hendrickbg/covid19_mon_track/Firmware_Project/Vaccine_Tracker_BLE/Drivers/Peripherals_Drivers/Inc/bluenrg_lp_hal_flash.h

/**
******************************************************************************
* @file    bluenrg_lp_hal_flash.h
* @author  RF Application Team
* @brief   Header file of FLASH HAL module.
******************************************************************************
* @attention
*
* <h2><center>&copy; Copyright (c) 2018 STMicroelectronics. 
* All rights reserved.</center></h2>
*
* This software component is licensed by ST under BSD 3-Clause license,
* the "License"; You may not use this file except in compliance with the 
* License. You may obtain a copy of the License at:
*                        opensource.org/licenses/BSD-3-Clause
*
******************************************************************************
*/

/* Define to prevent recursive inclusion -------------------------------------*/
#ifndef BLUENRG_LP_HAL_FLASH_H
#define BLUENRG_LP_HAL_FLASH_H

#ifdef __cplusplus
extern "C" {
#endif
  
  /* Includes ------------------------------------------------------------------*/
#include "bluenrg_lp_hal_def.h"
  
  /** @addtogroup BLUENRG_LP_HAL_Driver
  * @{
  */
  
  /** @addtogroup FLASH
  * @{
  */
  
  /* Exported types ------------------------------------------------------------*/
  /** @defgroup FLASH_Exported_Types FLASH Exported Types
  * @{
  */
  
  /**
  * @brief  FLASH Erase structure definition
  */
  typedef struct
  {
    uint32_t TypeErase;   /*!< Mass erase or page erase.
    This parameter can be a value of @ref FLASH_TYPE_ERASE */
    uint32_t Page;        /*!< Initial Flash page to erase when page erase is enabled
    This parameter must be a value between 0 and (max number of pages - 1) */
    uint32_t NbPages;     /*!< Number of pages to be erased.
    This parameter must be a value between 1 and (max number of pages - value of initial page)*/
  } FLASH_EraseInitTypeDef;
  
  /**
  * @brief  FLASH handle Structure definition
  */
  typedef struct
  {
    HAL_LockTypeDef   Lock;              /* FLASH locking object */
    uint32_t          ErrorCode;         /* FLASH error code */
    uint32_t          ProcedureOnGoing;  /* Internal variable to indicate which procedure is ongoing or not in IT context */
    uint32_t          Address;           /* Internal variable to save address selected for program in IT context */
    uint32_t          Page;              /* Internal variable to define the current page which is erasing in IT context */
    uint32_t          NbPagesToErase;    /* Internal variable to save the remaining pages to erase in IT context */
  } FLASH_ProcessTypeDef;
  
  /**
  * @}
  */
  
  /* Exported constants --------------------------------------------------------*/
  /** @defgroup FLASH_Exported_Constants FLASH Exported Constants
  * @{
  */
  
  /** @defgroup FLASH_WAIT_STATES FLASH Wait States
  * @{
  */
#define FLASH_WAIT_STATES_0                 0x00000000UL                /*!< FLASH Zero wait state   */
#define FLASH_WAIT_STATES_1                 FLASH_CONFIG_WAIT_STATES_0  /*!< FLASH One wait state    */
  /**
  * @}
  */
  
  /** @defgroup FLASH_CONFIG_IRQ_VECT_TABLE FLASH Configuration Interrupt Vector Table 
  * @{
  */
#define FLASH_CONFIG_IRQ_VECT_TABLE_FLASH    FLASH_CONFIG_PREMAP  /*!< Vector Table located in FLASH */
#define FLASH_CONFIG_IRQ_VECT_TABLE_RAM      FLASH_CONFIG_REMAP   /*!< Vector Table located in RAM   */
  /**
  * @}
  */
  
  /** @defgroup FLASH_FLAGS FLASH Flags Definition
  * @{
  */
#define FLASH_FLAG_CMDDONE             FLASH_IRQRAW_CMDDONE_RIS     /*!< FLASH command done flag    */
#define FLASH_FLAG_CMDSTART            FLASH_IRQRAW_CMDSTART_RIS    /*!< FLASH command started flag */
#define FLASH_FLAG_CMDERR              FLASH_IRQRAW_CMDERR_RIS      /*!< FLASH command error flag   */
#define FLASH_FLAG_ILLCMD              FLASH_IRQRAW_ILLCMD_RIS      /*!< FLASH illegal command flag */
  
#define FLASH_FLAG_ALL_ERRORS          (FLASH_IRQRAW_CMDERR_RIS | FLASH_IRQRAW_ILLCMD_RIS)
  
  /** @defgroup FLASH_INTERRUPT_DEFINITION FLASH Interrupts Definition
  * @brief FLASH Interrupt definition
  * @{
  */
#define FLASH_IT_CMDDONE               FLASH_IRQMASK_CMDDONEM     /*!< FLASH command done Interrupt source */
#define FLASH_IT_CMDSTART              FLASH_IRQMASK_CMDSTARTM    /*!< FLASH command started Interrupt source */
#define FLASH_IT_CMDERR                FLASH_IRQMASK_CMDERRM      /*!< FLASH command error Interrupt source */
#define FLASH_IT_ILLCMD                FLASH_IRQMASK_ILLCMDM      /*!< FLASH illegal command Interrupt source */
  /**
  * @}
  */
  
  /** @defgroup FLASH_ERROR FLASH Error
  * @{
  */
#define HAL_FLASH_ERROR_NONE            0x00000000U
#define HAL_FLASH_ERROR_OP              FLASH_FLAG_CMDERR
#define HAL_FLASH_ERROR_ILLCMD          FLASH_FLAG_ILLCMD
  /**
  * @}
  */
  
  /** @defgroup FLASH_COMMAND FLASH Command
  * @{
  */
#define FLASH_CMD_ERASE_PAGES           0x11  /*!< flash pages erase command */
#define FLASH_CMD_MASSERASE             0x22  /*!< Flash mass erase command  */
#define FLASH_CMD_WRITE                 0x33  /*!< Flash write command       */
#define FLASH_CMD_BURSTWRITE            0xCC  /*!< Flash burst write command */
#define FLASH_CMD_OTPWRITE              0xEE  /*!< Flash OTP write command   */
  /**
  * @}
  */
  
  /** @defgroup FLASH_TYPE_ERASE FLASH Erase Type
  * @{
  */
#define FLASH_TYPE_ERASE_PAGES           0x00  /*!< Pages erase      */
#define FLASH_TYPE_ERASE_MASSERASE       0xFF  /*!< Flash mass erase */
  /**
  * @}
  */
  
  /** @defgroup FLASH_PAGEPROT_GROUP FLASH write/page erase protection for group
  * @{
  */
#define FLASH_PAGEPROT_GROUP_15           (0x8000UL)		/*!< write/page erase protection for group 15 containing Flash pages 120 to 127 */
#define FLASH_PAGEPROT_GROUP_14           (0x4000UL)		/*!< write/page erase protection for group 14 containing Flash pages 112 to 119 */		
#define FLASH_PAGEPROT_GROUP_13           (0x2000UL)		/*!< write/page erase protection for group 13 containing Flash pages 104 to 111 */
#define FLASH_PAGEPROT_GROUP_12           (0x1000UL)		/*!< write/page erase protection for group 12 containing Flash pages 96 to 103  */		
#define FLASH_PAGEPROT_GROUP_11           (0x800UL)		/*!< write/page erase protection for group 11 containing Flash pages 88 to 95   */
#define FLASH_PAGEPROT_GROUP_10           (0x400UL)		/*!< write/page erase protection for group 10 containing Flash pages 80 to 87   */
#define FLASH_PAGEPROT_GROUP_9            (0x200UL)		/*!< write/page erase protection for group 9  containing Flash pages 72 to 79   */
#define FLASH_PAGEPROT_GROUP_8            (0x100UL)		/*!< write/page erase protection for group 8  containing Flash pages 64 to 71   */
#define FLASH_PAGEPROT_GROUP_7            (0x80UL)		/*!< write/page erase protection for group 7  containing Flash pages 56 to 63   */
#define FLASH_PAGEPROT_GROUP_6            (0x40UL)		/*!< write/page erase protection for group 6  containing Flash pages 48 to 55   */
#define FLASH_PAGEPROT_GROUP_5            (0x20UL)		/*!< write/page erase protection for group 5  containing Flash pages 40 to 47   */
#define FLASH_PAGEPROT_GROUP_4            (0x10UL)		/*!< write/page erase protection for group 4  containing Flash pages 32 to 39   */
#define FLASH_PAGEPROT_GROUP_3            (0x8UL)		/*!< write/page erase protection for group 3  containing Flash pages 24 to 31   */
#define FLASH_PAGEPROT_GROUP_2            (0x4UL)		/*!< write/page erase protection for group 2  containing Flash pages 16 to 23   */	    	
#define FLASH_PAGEPROT_GROUP_1            (0x2UL)		/*!< write/page erase protection for group 1  containing Flash pages 8 to 15    */
#define FLASH_PAGEPROT_GROUP_0            (0x1UL)		/*!< write/page erase protection for group 0  containing Flash pages 0 to 7     */ 
    /**
    * @}
    */
    
  
/**
  * @brief  Page Protection function configuration structure definition
  */
typedef struct
{
  uint32_t pageProt_0;       /*!< For cut 1.0 indicate the group to configure.
                                  - This parameter can be a value of @ref FLASH_PAGEPROT_GROUP                   
                                  For cut 2.0 it is a bitfield built as follows:
                                  - bit[6:0]   = SIZE: number of 2 kB pages to protect including the starting page
                                                       @ref pageProt_0 param (provided in the offset bits)
                                  - bit[7]     = reserved
                                  - bit[14:8]  = OFFSET: page number to start the write protection 
                                                        (value between 0 and 0x7F)
                                  - bit[15]    = reserved
                                  - bit[22:16] = SIZE: same meaning of bit[6:0]
                                  - bit[23]    = reserved
                                  - bit[30:24] = OFFSET: same meaning of bit[22:16]
                                  - bit[31]    = reserved                                                           */
  uint32_t pageProt_1;       /*!< Valid only for cut 2.0 same meaning of @ref pageProt_0 parameter                  */
  FunctionalState state;     /*!< The new state of the group.
                                  This parameter can be a value of @ref FunctionalState                             */
} FLASH_PageProtectionTypeDef;

  
    /**
    * @}
    */
    
    /* Exported macros -----------------------------------------------------------*/
    /** @defgroup FLASH_Exported_Macros FLASH Exported Macros
    *  @brief macros to control FLASH features
    *  @{
    */
    
    /**
    * @brief  Set the FLASH Wait States.
    * @param __WAIT_STATES__ FLASH WAIT States
    *         This parameter can be one of the following values :
    *     @arg @ref FLASH_WAIT_STATES_0 FLASH Zero wait state
    *     @arg @ref FLASH_WAIT_STATES_1 FLASH One wait state
    * @retval None
    */
#define __HAL_FLASH_SET_WAIT_STATES(__WAIT_STATES__)    MODIFY_REG(FLASH->CONFIG, FLASH_CONFIG_WAIT_STATES, (__WAIT_STATES__))
    
    /**
    * @brief  Get the FLASH Wait States.
    * @retval FLASH Wait States
    *         Returned value can be one of the following values :
    *     @arg @ref FLASH_WAIT_STATES_0 FLASH Zero wait state
    *     @arg @ref FLASH_WAIT_STATES_1 FLASH One wait state
    */ 
#define __HAL_FLASH_GET_WAIT_STATES()               READ_BIT(FLASH->CONFIG, FLASH_CONFIG_WAIT_STATES)
    
    /**
    * @brief  Enable the FLASH burst write operations.
    * @retval None
    */
#define __HAL_FLASH_BURSTWRITE_ENABLE()    CLEAR_BIT(FLASH->CONFIG, FLASH_CONFIG_DIS_GROUP_WRITE)
    
    /**
    * @brief  Disable the FLASH burst write operations.
    * @retval None
    */
#define __HAL_FLASH_BURSTWRITE_DISABLE()    SET_BIT(FLASH->CONFIG, FLASH_CONFIG_DIS_GROUP_WRITE)
    
    /**
    * @brief  Set the FLASH Interrupt Vector Table location.
    * @param __VECT_TABLE__ Vector Table Configuration
    *         This parameter can be one of the following values :
    *     @arg @ref FLASH_CONFIG_IRQ_VECT_TABLE_FLASH Vector Table located in FLASH
    *     @arg @ref FLASH_CONFIG_IRQ_VECT_TABLE_RAM   Vector Table located in RAM
    * @retval None
    */
#define __HAL_FLASH_SET_VECT_TABLE(__VECT_TABLE__)    MODIFY_REG(FLASH->CONFIG, FLASH_CONFIG_PREMAP|FLASH_CONFIG_REMAP, (__VECT_TABLE__))
    
    /**
    * @brief  Get the FLASH Interrupt Vector Table location.
    * @retval Vector Table Configuration
    *         Returned value can be one of the following values :
    *     @arg @ref FLASH_CONFIG_IRQ_VECT_TABLE_FLASH Vector Table located in FLASH
    *     @arg @ref FLASH_CONFIG_IRQ_VECT_TABLE_RAM   Vector Table located in RAM
    */ 
#define __HAL_FLASH_GET_VECT_TABLE()               READ_BIT(FLASH->CONFIG, FLASH_CONFIG_PREMAP|FLASH_CONFIG_REMAP)
    
    /**
    * @}
    */
    
    /** @defgroup FLASH_Interrupt FLASH Interrupts Macros
    *  @brief macros to handle FLASH interrupts
    * @{
    */
    
    /**
    * @brief  Enable the specified FLASH interrupt.
    * @param __INTERRUPT__ FLASH interrupt
    *         This parameter can be any combination of the following values:
    *     @arg @ref FLASH_IT_CMDDONE  Command Done Interrupt
    *     @arg @ref FLASH_IT_CMDSTART Command Started Interrupt
    *     @arg @ref FLASH_IT_CMDERR   Command Error Interrupt
    *     @arg @ref FLASH_IT_ILLCMD   Illegal Command Interrupt
    * @retval none
    */
#define __HAL_FLASH_ENABLE_IT(__INTERRUPT__)    SET_BIT(FLASH->IRQMASK, (__INTERRUPT__))
    
    /**
    * @brief  Disable the specified FLASH interrupt.
    * @param __INTERRUPT__ FLASH interrupt
    *         This parameter can be any combination of the following values:
    *     @arg @ref FLASH_IT_CMDDONE  Command Done Interrupt
    *     @arg @ref FLASH_IT_CMDSTART Command Started Interrupt
    *     @arg @ref FLASH_IT_CMDERR   Command Error Interrupt
    *     @arg @ref FLASH_IT_ILLCMD   Illegal Command Interrupt
    * @retval none
    */
#define __HAL_FLASH_DISABLE_IT(__INTERRUPT__)   CLEAR_BIT(FLASH->IRQMASK, (__INTERRUPT__))
    
    /**
    * @brief  Check whether the specified FLASH interrupt has occurred or not.
    * @param __INTERRUPT__ FLASH interrupt
    *         This parameter can be any combination of the following values:
    *     @arg @ref FLASH_IT_CMDDONE  Command Done Interrupt
    *     @arg @ref FLASH_IT_CMDSTART Command Started Interrupt
    *     @arg @ref FLASH_IT_CMDERR   Command Error Interrupt
    *     @arg @ref FLASH_IT_ILLCMD   Illegal Command Interrupt
    * @retval The new state of __INTERRUPT__ (SET or RESET).
    */
#define __HAL_FLASH_GET_IT(__INTERRUPT__)   ((READ_BIT(FLASH->IRQSTAT, (__INTERRUPT__)) != RESET) ? SET : RESET)
    
    /**
    * @brief Clear the specified FLASH interrupt flag.
    * @param __INTERRUPT__ FLASH interrupt
    *         This parameter can be any combination of the following values:
    *     @arg @ref FLASH_IT_CMDDONE  Command Done Interrupt
    *     @arg @ref FLASH_IT_CMDSTART Command Started Interrupt
    *     @arg @ref FLASH_IT_CMDERR   Command Error Interrupt
    *     @arg @ref FLASH_IT_ILLCMD   Illegal Command Interrupt
    * @retval None
    */
#define __HAL_FLASH_CLEAR_IT(__INTERRUPT__)   SET_BIT(FLASH->IRQSTAT, (__INTERRUPT__))
    
    /**
    * @brief  Check whether the specified FLASH flag is set or not.
    * @param __FLAG__ specifies the FLASH flag to check.
    *   This parameter can be one of the following values:
    *     @arg @ref FLASH_FLAG_CMDDONE     FLASH command done flag
    *     @arg @ref FLASH_FLAG_CMDSTART    FLASH command started flag
    *     @arg @ref FLASH_FLAG_CMDERR      FLASH command error flag
    *     @arg @ref FLASH_FLAG_ILLCMD      FLASH illegal command flag
    * @retval The new state of FLASH_FLAG (SET or RESET).
    */
#define __HAL_FLASH_GET_FLAG(__FLAG__)  ((READ_BIT(FLASH->IRQRAW, (__FLAG__)) == (__FLAG__)) ? 1UL : 0UL)
    
    /**
    * @brief  Clear the FLASH's pending flags.
    * @param __FLAG__ specifies the FLASH flags to clear.
    *   This parameter can be any combination of the following values:
    *     @arg @ref FLASH_FLAG_CMDDONE     FLASH command done flag
    *     @arg @ref FLASH_FLAG_CMDSTART    FLASH command started flag
    *     @arg @ref FLASH_FLAG_CMDERR      FLASH command error flag
    *     @arg @ref FLASH_FLAG_ILLCMD      FLASH illegal command flag
    * @retval None
    */
#define __HAL_FLASH_CLEAR_FLAG(__FLAG__) (SET_BIT(FLASH->IRQRAW, (__FLAG__)))
    /**
    * @}
    */
    
    /* Include FLASH HAL Extended module */
#include "bluenrg_lp_hal_flash_ex.h"
    
    /* Exported variables --------------------------------------------------------*/
    /** @defgroup FLASH_Exported_Variables FLASH Exported Variables
    * @{
    */
    extern FLASH_ProcessTypeDef pFlash;
  /**
  * @}
  */
  
  /* Exported functions --------------------------------------------------------*/
  /** @addtogroup FLASH_Exported_Functions
  * @{
  */
  
  /* Program operation functions  ***********************************************/
  /** @addtogroup FLASH_Exported_Functions_Group1
  * @{
  */
  HAL_StatusTypeDef  HAL_FLASH_Program(uint32_t Address, uint32_t Data);
  HAL_StatusTypeDef  HAL_FLASH_Program_IT(uint32_t Address, uint32_t Data);
  HAL_StatusTypeDef  HAL_FLASH_ProgramBurst(uint32_t Address, uint32_t *Data);
  HAL_StatusTypeDef  HAL_FLASH_ProgramBurst_IT(uint32_t Address, uint32_t *Data);
  /* FLASH IRQ handler method */
  void               HAL_FLASH_IRQHandler(void);
  /* Callbacks in non blocking modes */
  void               HAL_FLASH_EndOfOperationCallback(uint32_t ReturnValue);
  void               HAL_FLASH_OperationErrorCallback(uint32_t ReturnValue);
  /**
  * @}
  */
  
  /* Peripheral State functions  ************************************************/
  /** @addtogroup FLASH_Exported_Functions_Group2
  * @{
  */
  uint32_t HAL_FLASH_GetError(void);
  /**
  * @}
  */
  
  /**
  * @}
  */
  
  /* Private types --------------------------------------------------------*/
  /** @defgroup FLASH_Private_types FLASH Private Types
  * @{
  */
  HAL_StatusTypeDef  FLASH_WaitForLastOperation(uint32_t Timeout);
  /**
  * @}
  */
  
  /* Private constants --------------------------------------------------------*/
  /** @defgroup FLASH_Private_Constants FLASH Private Constants
  * @{
  */
#define FLASH_SIZE                      (((*(uint32_t *)FLASHSIZE_BASE & 0xFFFF) + 1) << 2U)
#define FLASH_START_ADDR                NVM_BASE
#define FLASH_END_ADDR                  (FLASH_START_ADDR + FLASH_SIZE - 1U)
 
 
#define FLASH_PAGE_SIZE                 0x00000800U  /*!< FLASH Page Size, 2KBytes */
#define FLASH_PAGE_NUMBER               (FLASH_SIZE/FLASH_PAGE_SIZE )
#define FLASH_TIMEOUT_VALUE             1000U        /*!< FLASH Execution Timeout, 1 s */
  
#define FLASH_WRERP_GRANULARITY         0x00004000U  /*!< FLASH Write/Erase Protection Granularity, 16KBytes */
#define FLASH_PCROP_GRANULARITY         FLASH_SIZE   /*!< FLASH Code Readout Protection Granularity, all the MAIN FLASH */
  
#define FLASH_TYPENONE                  0x00000000u  /*!< No Programming Procedure On Going */
  
  /**
  * @}
  */
  
  /* Private macros ------------------------------------------------------------*/
  /** @defgroup FLASH_Private_Macros FLASH Private Macros
  *  @{
  */
  
#define IS_FLASH_MAIN_MEM_ADDRESS(__VALUE__)        (((__VALUE__) >= FLASH_START_ADDR) && ((__VALUE__) <= FLASH_END_ADDR))
  
#define IS_FLASH_PROGRAM_MAIN_MEM_ADDRESS(__VALUE__)   (((__VALUE__) >= FLASH_START_ADDR) && ((__VALUE__) <= (FLASH_START_ADDR + FLASH_SIZE - 4UL)) && (((__VALUE__) % 4UL) == 0UL))
  
#define IS_FLASH_PROGRAM_OTP_ADDRESS(__VALUE__)     (((__VALUE__) >= OTP_AREA_BASE) && ((__VALUE__) <= (OTP_AREA_END_ADDR + 1UL - 4UL)) && (((__VALUE__) % 4UL) == 0UL))
  
#define IS_FLASH_PROGRAM_ADDRESS(__VALUE__)         ((IS_FLASH_PROGRAM_MAIN_MEM_ADDRESS(__VALUE__)) || (IS_FLASH_PROGRAM_OTP_ADDRESS(__VALUE__)))
  
#define IS_FLASH_PAGE(__VALUE__)                    ((__VALUE__) <= FLASH_PAGE_NUMBER)
  
#define IS_ADDR_ALIGNED_32BITS(__VALUE__)           (((__VALUE__) & ~0x3U) == (__VALUE__))
  
#define IS_FLASH_WAIT_STATES(__VALUE__)              (((__VALUE__) == FLASH_WAIT_STATES_0) || \
  ((__VALUE__) == FLASH_WAIT_STATES_1))

#define IS_FLASH_TYPE_ERASE(__VALUE__)               (((__VALUE__) == FLASH_TYPE_ERASE_PAGES) || \
((__VALUE__) == FLASH_TYPE_ERASE_MASSERASE))

/**
* @}
*/

/**
* @}
*/

/**
* @}
*/

#ifdef __cplusplus
}
#endif

#endif /* BLUENRG_LP_HAL_FLASH_H */

/************************ (C) COPYRIGHT STMicroelectronics *****END OF FILE****/
