hendrickbg/covid19_mon_track/Firmware_Project/Vaccine_Tracker_BLE/Drivers/Peripherals_Drivers/Src/bluenrg_lp_hal.c

/**
  ******************************************************************************
  * @file    bluenrg_lp_hal.c
  * @author  RF Application Team
  * @brief   HAL module driver.
  *          This is the common part of the HAL initialization
  *
  @verbatim
  ==============================================================================
                     ##### How to use this driver #####
  ==============================================================================
    [..]
    The common HAL driver contains a set of generic and common APIs that can be
    used by the PPP peripheral drivers and the user to start using the HAL.
    [..]
    The HAL contains two APIs' categories:
         (+) Common HAL APIs
         (+) Services HAL APIs

  @endverbatim
  ******************************************************************************
  * @attention
  *
  * <h2><center>&copy; Copyright (c) 2018 STMicroelectronics. 
  * All rights reserved.</center></h2>
  *
  * This software component is licensed by ST under BSD 3-Clause license,
  * the "License"; You may not use this file except in compliance with the 
  * License. You may obtain a copy of the License at:
  *                        opensource.org/licenses/BSD-3-Clause
  *
  ******************************************************************************
  */

/* Includes ------------------------------------------------------------------*/
#include "bluenrg_lp_hal.h"

/** @addtogroup BLUENRG_LP_HAL_Driver
  * @{
  */

/** @addtogroup HAL
  * @brief HAL module driver
  * @{
  */

#ifdef HAL_MODULE_ENABLED

/* Private typedef -----------------------------------------------------------*/
/* Private define ------------------------------------------------------------*/

/** @defgroup HAL_Private_Constants HAL Private Constants
  * @{
  */
/**
 * @brief BLUENRG_LP HAL Driver version number
   */
#define __BLUENRG_LP_HAL_VERSION_MAIN   (0x00U) /*!< [31:24] main version */
#define __BLUENRG_LP_HAL_VERSION_SUB1   (0x00U) /*!< [23:16] sub1 version */
#define __BLUENRG_LP_HAL_VERSION_SUB2   (0x0DU) /*!< [15:8]  sub2 version */
#define __BLUENRG_LP_HAL_VERSION_RC     (0x00U) /*!< [7:0]  release candidate */
#define __BLUENRG_LP_HAL_VERSION         ((__BLUENRG_LP_HAL_VERSION_MAIN << 24U)\
                                        |(__BLUENRG_LP_HAL_VERSION_SUB1 << 16U)\
                                        |(__BLUENRG_LP_HAL_VERSION_SUB2 << 8U )\
                                        |(__BLUENRG_LP_HAL_VERSION_RC))

/**
  * @}
  */

/* Private macro -------------------------------------------------------------*/
/* Exported variables ---------------------------------------------------------*/
/** @defgroup HAL_Exported_Variables HAL Exported Variables
  * @{
  */
__IO uint32_t uwTick;
uint32_t uwTickPrio = (1UL << __NVIC_PRIO_BITS); /* Invalid PRIO */
uint32_t uwTickFreq = HAL_TICK_FREQ_DEFAULT;  /* 1KHz */
/**
  * @}
  */

/* Private function prototypes -----------------------------------------------*/
/* Exported functions --------------------------------------------------------*/

/** @addtogroup HAL_Exported_Functions
  * @{
  */

/** @addtogroup HAL_Exported_Functions_Group1
 *  @brief    HAL Initialization and Configuration functions
 *
@verbatim
 ===============================================================================
           ##### HAL Initialization and Configuration functions #####
 ===============================================================================
    [..]  This section provides functions allowing to:
      (+) Initialize the Flash interface the NVIC allocation and initial time base
          clock configuration.
      (+) De-initialize common part of the HAL.
      (+) Configure the time base source to have 1ms time base with a dedicated
          Tick interrupt priority.
        (++) SysTick timer is used by default as source of time base, but user
             can eventually implement his proper time base source (a general purpose
             timer for example or other time source), keeping in mind that Time base
             duration should be kept 1ms since PPP_TIMEOUT_VALUEs are defined and
             handled in milliseconds basis.
        (++) Time base configuration function (HAL_InitTick ()) is called automatically
             at the beginning of the program after reset by HAL_Init() or at any time
             when clock is configured, by HAL_RCC_ClockConfig().
        (++) Source of time base is configured  to generate interrupts at regular
             time intervals. Care must be taken if HAL_Delay() is called from a
             peripheral ISR process, the Tick interrupt line must have higher priority
            (numerically lower) than the peripheral interrupt. Otherwise the caller
            ISR process will be blocked.
       (++) functions affecting time base configurations are declared as __weak
             to make  override possible  in case of other  implementations in user file.
@endverbatim
  * @{
  */

/**
  * @brief  This function is used to initialize the HAL Library; it must be the first
  *         instruction to be executed in the main program (before to call any other
  *         HAL function), it performs the following:
  *           Configures the SysTick to generate an interrupt each 1 millisecond,
  *           which is clocked by the System Clock.
  *           Calls the HAL_MspInit() callback function defined in user file
  *           "bluenrg_lp_hal_msp.c" to do the global low level hardware initialization
  *
  * @note   SysTick is used as time base for the HAL_Delay() function, the application
  *         need to ensure that the SysTick time base is always set to 1 millisecond
  *         to have correct HAL operation.
  * @retval HAL status
  */
HAL_StatusTypeDef HAL_Init(void)
{
  HAL_StatusTypeDef  status = HAL_OK;
  
  /* Use SysTick as time base source and configure 1ms tick (default clock after Reset is MSI) */
  if (HAL_InitTick(TICK_INT_PRIORITY) != HAL_OK)
  {
    status = HAL_ERROR;
  }
  else
  {
    /* Init the low level hardware */
    HAL_MspInit();
  }

  /* Return function status */
  return status;
}

/**
  * @brief  This function de-Initializes common part of the HAL and stops the source of time base.
  * @note   This function is optional.
  * @retval HAL status
  */
HAL_StatusTypeDef HAL_DeInit(void)
{
  /* Reset of all peripherals */
  __HAL_RCC_AHB_FORCE_RESET();
  __HAL_RCC_AHB_RELEASE_RESET();

  __HAL_RCC_APB0_FORCE_RESET();
  __HAL_RCC_APB0_RELEASE_RESET();

  __HAL_RCC_APB1_FORCE_RESET();
  __HAL_RCC_APB1_RELEASE_RESET();

  __HAL_RCC_APB2_FORCE_RESET();
  __HAL_RCC_APB2_RELEASE_RESET();

  /* De-Init the low level hardware */
  HAL_MspDeInit();

  /* Return function status */
  return HAL_OK;
}

/**
  * @brief  Initialize the MSP.
  * @retval None
  */
WEAK_FUNCTION(void HAL_MspInit(void))
{   
  /* NOTE : This function should not be modified, when the callback is needed,
            the HAL_MspInit could be implemented in the user file
   */
}

/**
  * @brief  DeInitializes the MSP.
  * @retval None
  */
WEAK_FUNCTION(void HAL_MspDeInit(void))
{     
  /* NOTE : This function should not be modified, when the callback is needed,
            the HAL_MspDeInit could be implemented in the user file
   */
}

/**
  * @brief This function configures the source of the time base:
  *        The time source is configured  to have 1ms time base with a dedicated
  *        Tick interrupt priority.
  * @note This function is called  automatically at the beginning of program after
  *       reset by HAL_Init() or at any time when clock is reconfigured  by HAL_RCC_ClockConfig().
  * @note In the default implementation, SysTick timer is the source of time base.
  *       It is used to generate interrupts at regular time intervals.
  *       Care must be taken if HAL_Delay() is called from a peripheral ISR process,
  *       The SysTick interrupt must have higher priority (numerically lower)
  *       than the peripheral interrupt. Otherwise the caller ISR process will be blocked.
  *       The function is declared as __weak  to be overwritten  in case of other
  *       implementation  in user file.
  * @param TickPriority Tick interrupt priority.
  * @retval HAL status
  */
WEAK_FUNCTION(HAL_StatusTypeDef HAL_InitTick(uint32_t TickPriority))
{
  HAL_StatusTypeDef  status = HAL_OK;

  if (uwTickFreq != 0U)
  {
    /*Configure the SysTick to have interrupt in 1ms time basis*/
    if (HAL_SYSTICK_Config(HAL_RCC_GetSysClockFreq()/ (1000U /uwTickFreq)) == 0U)
    {
      /* Configure the SysTick IRQ priority */
      if (TickPriority < (1UL << __NVIC_PRIO_BITS))
      {
        HAL_NVIC_SetPriority(SysTick_IRQn, TickPriority);
        uwTickPrio = TickPriority;
      }
      else
      {
        status = HAL_ERROR;
      }
    }
    else
    {  
      status = HAL_ERROR;
    }
  }
  else
  {
    status = HAL_ERROR;
  }

  /* Return function status */
  return status;
}

/**
  * @}
  */

/** @addtogroup HAL_Exported_Functions_Group2
 *  @brief    HAL Control functions
 *
@verbatim
 ===============================================================================
                      ##### HAL Control functions #####
 ===============================================================================
    [..]  This section provides functions allowing to:
      (+) Provide a tick value in millisecond
      (+) Provide a blocking delay in millisecond
      (+) Suspend the time base source interrupt
      (+) Resume the time base source interrupt
      (+) Get the HAL API driver version
      (+) Get the device revision identifier
      (+) Get the device identifier
      (+) Get the unique device identifier

@endverbatim
  * @{
  */

/**
  * @brief This function is called to increment  a global variable "uwTick"
  *        used as application time base.
  * @note In the default implementation, this variable is incremented each 1ms
  *       in SysTick ISR.
 * @note This function is declared as __weak to be overwritten in case of other
  *      implementations in user file.
  * @retval None
  */
WEAK_FUNCTION(void HAL_IncTick(void))
{
  uwTick += (uint32_t)uwTickFreq;
}

/**
  * @brief Provides a tick value in millisecond.
  * @note This function is declared as __weak to be overwritten in case of other
  *       implementations in user file.
  * @retval tick value
  */
WEAK_FUNCTION(uint32_t HAL_GetTick(void))
{
  return uwTick;
}

/**
  * @brief This function returns a tick priority.
  * @retval tick priority
  */
uint32_t HAL_GetTickPrio(void)
{
  return uwTickPrio;
}

/**
  * @brief Set new tick Freq.
  * @retval Status
  */
HAL_StatusTypeDef HAL_SetTickFreq(uint32_t Freq)
{
  HAL_StatusTypeDef status  = HAL_OK;
  assert_param(IS_TICKFREQ(Freq));

  if (uwTickFreq != Freq)
  {
    uwTickFreq = Freq;

    /* Apply the new tick Freq  */
    status = HAL_InitTick(uwTickPrio);
  }

  return status;
}

/**
  * @brief Return tick frequency.
  * @retval tick period in Hz
  */
uint32_t HAL_GetTickFreq(void)
{
  return uwTickFreq;
}

/**
  * @brief This function provides minimum delay (in milliseconds) based 
  *        on variable incremented. 
  * @note In the default implementation , SysTick timer is the source of time base.
  *       It is used to generate interrupts at regular time intervals where uwTick
  *       is incremented.
  * @note This function is declared as __weak to be overwritten in case of other
  *       implementations in user file.
  * @param Delay  specifies the delay time length, in milliseconds.
  * @retval None
  */
void HAL_Delay(uint32_t Delay)
{
    uint32_t tickstart = HAL_GetTick();
    uint32_t wait = Delay;
  
    /* Add a freq to guarantee minimum wait */
    if (wait < HAL_MAX_DELAY)
    {
      wait += (uint32_t)(uwTickFreq);
    }
  
    while ((HAL_GetTick() - tickstart) < wait)
    {
    }
}


/**
  * @brief Suspend Tick increment.
  * @note In the default implementation , SysTick timer is the source of time base. It is
  *       used to generate interrupts at regular time intervals. Once HAL_SuspendTick()
  *       is called, the SysTick interrupt will be disabled and so Tick increment
  *       is suspended.
  * @note This function is declared as __weak to be overwritten in case of other
  *       implementations in user file.
  * @retval None
  */
WEAK_FUNCTION(void HAL_SuspendTick(void))
{
  /* Disable SysTick Interrupt */
  CLEAR_BIT(SysTick->CTRL,SysTick_CTRL_TICKINT_Msk);
}

/**
  * @brief Resume Tick increment.
  * @note In the default implementation , SysTick timer is the source of time base. It is
  *       used to generate interrupts at regular time intervals. Once HAL_ResumeTick()
  *       is called, the SysTick interrupt will be enabled and so Tick increment
  *       is resumed.
  * @note This function is declared as __weak to be overwritten in case of other
  *       implementations in user file.
  * @retval None
  */
WEAK_FUNCTION(void HAL_ResumeTick(void))
{
  /* Enable SysTick Interrupt */
  SET_BIT(SysTick->CTRL,SysTick_CTRL_TICKINT_Msk);
}

/**
  * @brief  Returns the HAL revision
  * @retval version : 0xXYZR (8bits for each decimal, R for RC)
  */
uint32_t HAL_GetHalVersion(void)
{
 return __BLUENRG_LP_HAL_VERSION;
}

/**
  * @brief  Returns the device device identifier.
  * @retval Device identifier
  */
uint32_t HAL_GetDEVID(void)
{
  return(LL_SYSCFG_GetDeviceID());
}

/**
  * @brief  Return the first word of the unique device identifier (UID based on 64 bits)
  * @retval Device identifier
  */
uint32_t HAL_GetUIDw0(void)
{
  return(READ_REG(*((uint32_t *)UID64_BASE)));
}

/**
  * @brief  Return the second word of the unique device identifier (UID based on 64 bits)
  * @retval Device identifier
  */
uint32_t HAL_GetUIDw1(void)
{
  return(READ_REG(*((uint32_t *)(UID64_BASE + 4U))));
}


/**
  * @}
  */

/**
  * @}
  */

#endif /* HAL_MODULE_ENABLED */
/**
  * @}
  */

/**
  * @}
  */

/************************ (C) COPYRIGHT STMicroelectronics *****END OF FILE****/
