hendrickbg/covid19_mon_track/Firmware_Project/HT32SX_Firmware/AT_Commands/STM32CubeIDE/Core/Src/usart.c

/**
  ******************************************************************************
  * File Name          : USART.c
  * Description        : This file provides code for the configuration
  *                      of the USART instances.
  ******************************************************************************
  * @attention
  *
  * <h2><center>&copy; Copyright (c) 2021 STMicroelectronics.
  * All rights reserved.</center></h2>
  *
  * This software component is licensed by ST under BSD 3-Clause license,
  * the "License"; You may not use this file except in compliance with the
  * License. You may obtain a copy of the License at:
  *                        opensource.org/licenses/BSD-3-Clause
  *
  ******************************************************************************
  */

/* Includes ------------------------------------------------------------------*/
#include "usart.h"

/* USER CODE BEGIN 0 */
#include "dma.h"

uint8_t DMA_RX_Buffer[DMA_RX_BUFFER_SIZE];
/* USER CODE END 0 */

UART_HandleTypeDef huart1;
UART_HandleTypeDef huart2;
DMA_HandleTypeDef hdma_usart1_rx;
DMA_HandleTypeDef hdma_usart1_tx;

/* USART1 init function */

void MX_USART1_UART_Init(void)
{

  huart1.Instance = USART1;
  huart1.Init.BaudRate = 115200;
  huart1.Init.WordLength = UART_WORDLENGTH_8B;
  huart1.Init.StopBits = UART_STOPBITS_1;
  huart1.Init.Parity = UART_PARITY_NONE;
  huart1.Init.Mode = UART_MODE_TX_RX;
  huart1.Init.HwFlowCtl = UART_HWCONTROL_NONE;
  huart1.Init.OverSampling = UART_OVERSAMPLING_16;
  huart1.Init.OneBitSampling = UART_ONE_BIT_SAMPLE_DISABLE;
  huart1.AdvancedInit.AdvFeatureInit = UART_ADVFEATURE_NO_INIT;
  if (HAL_UART_Init(&huart1) != HAL_OK)
  {
    Error_Handler();
  }

}
/* USART2 init function */

void MX_USART2_UART_Init(void)
{

  huart2.Instance = USART2;
  huart2.Init.BaudRate = 115200;
  huart2.Init.WordLength = UART_WORDLENGTH_8B;
  huart2.Init.StopBits = UART_STOPBITS_1;
  huart2.Init.Parity = UART_PARITY_NONE;
  huart2.Init.Mode = UART_MODE_TX_RX;
  huart2.Init.HwFlowCtl = UART_HWCONTROL_NONE;
  huart2.Init.OverSampling = UART_OVERSAMPLING_16;
  huart2.Init.OneBitSampling = UART_ONE_BIT_SAMPLE_DISABLE;
  huart2.AdvancedInit.AdvFeatureInit = UART_ADVFEATURE_NO_INIT;
  if (HAL_UART_Init(&huart2) != HAL_OK)
  {
    Error_Handler();
  }

}

void HAL_UART_MspInit(UART_HandleTypeDef* uartHandle)
{

  GPIO_InitTypeDef GPIO_InitStruct = {0};
  if(uartHandle->Instance==USART1)
  {
    /* USART1 clock enable */
    __HAL_RCC_USART1_CLK_ENABLE();
  
    __HAL_RCC_GPIOA_CLK_ENABLE();
    /**USART1 GPIO Configuration    
    PA10     ------> USART1_RX
    PA9     ------> USART1_TX 
    */
    GPIO_InitStruct.Pin = GPIO_PIN_10|GPIO_PIN_9;
    GPIO_InitStruct.Mode = GPIO_MODE_AF_PP;
    GPIO_InitStruct.Pull = GPIO_NOPULL;
    GPIO_InitStruct.Speed = GPIO_SPEED_FREQ_VERY_HIGH;
    GPIO_InitStruct.Alternate = GPIO_AF4_USART1;
    HAL_GPIO_Init(GPIOA, &GPIO_InitStruct);

    /* USART1 DMA Init */
    /* USART1_RX Init */
    hdma_usart1_rx.Instance = DMA1_Channel5;
    hdma_usart1_rx.Init.Request = DMA_REQUEST_3;
    hdma_usart1_rx.Init.Direction = DMA_PERIPH_TO_MEMORY;
    hdma_usart1_rx.Init.PeriphInc = DMA_PINC_DISABLE;
    hdma_usart1_rx.Init.MemInc = DMA_MINC_ENABLE;
    hdma_usart1_rx.Init.PeriphDataAlignment = DMA_PDATAALIGN_BYTE;
    hdma_usart1_rx.Init.MemDataAlignment = DMA_MDATAALIGN_BYTE;
    hdma_usart1_rx.Init.Mode = DMA_CIRCULAR;
    hdma_usart1_rx.Init.Priority = DMA_PRIORITY_LOW;
    if (HAL_DMA_Init(&hdma_usart1_rx) != HAL_OK)
    {
      Error_Handler();
    }

    __HAL_LINKDMA(uartHandle,hdmarx,hdma_usart1_rx);

    /* USART1_TX Init */
    hdma_usart1_tx.Instance = DMA1_Channel4;
    hdma_usart1_tx.Init.Request = DMA_REQUEST_3;
    hdma_usart1_tx.Init.Direction = DMA_MEMORY_TO_PERIPH;
    hdma_usart1_tx.Init.PeriphInc = DMA_PINC_DISABLE;
    hdma_usart1_tx.Init.MemInc = DMA_MINC_ENABLE;
    hdma_usart1_tx.Init.PeriphDataAlignment = DMA_PDATAALIGN_BYTE;
    hdma_usart1_tx.Init.MemDataAlignment = DMA_MDATAALIGN_BYTE;
    hdma_usart1_tx.Init.Mode = DMA_NORMAL;
    hdma_usart1_tx.Init.Priority = DMA_PRIORITY_HIGH;
    if (HAL_DMA_Init(&hdma_usart1_tx) != HAL_OK)
    {
      Error_Handler();
    }

    __HAL_LINKDMA(uartHandle,hdmatx,hdma_usart1_tx);

    /* USART1 interrupt Init */
    HAL_NVIC_SetPriority(USART1_IRQn, 2, 0);
    HAL_NVIC_EnableIRQ(USART1_IRQn);
  }
  else if(uartHandle->Instance==USART2)
  {
    /* USART2 clock enable */
    __HAL_RCC_USART2_CLK_ENABLE();
  
    __HAL_RCC_GPIOA_CLK_ENABLE();
    /**USART2 GPIO Configuration    
    PA2     ------> USART2_TX
    PA3     ------> USART2_RX 
    */
    GPIO_InitStruct.Pin = GPIO_PIN_2|GPIO_PIN_3;
    GPIO_InitStruct.Mode = GPIO_MODE_AF_PP;
    GPIO_InitStruct.Pull = GPIO_NOPULL;
    GPIO_InitStruct.Speed = GPIO_SPEED_FREQ_VERY_HIGH;
    GPIO_InitStruct.Alternate = GPIO_AF4_USART2;
    HAL_GPIO_Init(GPIOA, &GPIO_InitStruct);

  }
}

void HAL_UART_MspDeInit(UART_HandleTypeDef* uartHandle)
{

  if(uartHandle->Instance==USART1)
  {
    /* Peripheral clock disable */
    __HAL_RCC_USART1_CLK_DISABLE();
  
    /**USART1 GPIO Configuration    
    PA10     ------> USART1_RX
    PA9     ------> USART1_TX 
    */
    HAL_GPIO_DeInit(GPIOA, GPIO_PIN_10|GPIO_PIN_9);

    /* USART1 DMA DeInit */
    HAL_DMA_DeInit(uartHandle->hdmarx);
    HAL_DMA_DeInit(uartHandle->hdmatx);

    /* USART1 interrupt Deinit */
    HAL_NVIC_DisableIRQ(USART1_IRQn);
  }
  else if(uartHandle->Instance==USART2)
  {
    /* Peripheral clock disable */
    __HAL_RCC_USART2_CLK_DISABLE();
  
    /**USART2 GPIO Configuration    
    PA2     ------> USART2_TX
    PA3     ------> USART2_RX 
    */
    HAL_GPIO_DeInit(GPIOA, GPIO_PIN_2|GPIO_PIN_3);

  }
} 

/* USER CODE BEGIN 1 */


void AT_USART_ResetUsart(void) {
	HAL_UART_MspDeInit(&huart1);
	HAL_Delay(10);

	MX_USART1_UART_Init();
	//HAL_UART_MspInit(&huart1);
	__HAL_UART_DISABLE(&huart1);
	__HAL_UART_ENABLE(&huart1);

	MX_DMA_Init();
}

void HW_UART_RESET_RXNEIE_Flag(void) {
	CLEAR_BIT(huart1.Instance->CR1, USART_CR1_RXNEIE);
}

void HW_UART_IDLE_IT_Config(void) {

	__HAL_UART_ENABLE_IT(&huart1, UART_IT_IDLE);   // enable idle line interrupt
	__HAL_DMA_ENABLE_IT (&hdma_usart1_rx, DMA_IT_TC);  // enable DMA Tx cplt interrupt

	hdma_usart1_rx.Instance->CCR &= 0xFFFFFFFB;
}

void HW_Config_Circular_DMA(void) {
	MX_USART1_UART_Init();
	HW_UART_RESET_RXNEIE_Flag();
	HW_UART_IDLE_IT_Config();

	HAL_UART_Receive_DMA(&huart1, DMA_RX_Buffer, DMA_RX_BUFFER_SIZE);
}

UART_HandleTypeDef * getUsartHandle(void) {
	return &huart1;
}

int __io_putchar(int ch) {
	HAL_UART_Transmit(&huart1, (uint8_t *)&ch, 1, 0xFFFF);
	return ch;
}

void printUart(char *str) {
	HAL_UART_Transmit(&huart2, (uint8_t *)str, strlen(str), 0xFFFF);
}

/* USER CODE END 1 */

/************************ (C) COPYRIGHT STMicroelectronics *****END OF FILE****/
