hendrickbg/covid19_mon_track/Firmware_Project/HT32SX_Firmware/AT_Commands/STM32CubeIDE/Core/Src/rtc.c

/**
  ******************************************************************************
  * File Name          : RTC.c
  * Description        : This file provides code for the configuration
  *                      of the RTC instances.
  ******************************************************************************
  * @attention
  *
  * <h2><center>&copy; Copyright (c) 2021 STMicroelectronics.
  * All rights reserved.</center></h2>
  *
  * This software component is licensed by ST under BSD 3-Clause license,
  * the "License"; You may not use this file except in compliance with the
  * License. You may obtain a copy of the License at:
  *                        opensource.org/licenses/BSD-3-Clause
  *
  ******************************************************************************
  */

/* Includes ------------------------------------------------------------------*/
#include "rtc.h"

/* USER CODE BEGIN 0 */
static volatile uint8_t rtc_irq = 0;
static volatile uint8_t rtc_in_use = 0;
static volatile uint8_t rtc_in_use_for_cs = 0;

static volatile uint32_t next_rtc_wakeup = 0;
static volatile uint16_t rtc_presc=2375;

/* USER CODE END 0 */

RTC_HandleTypeDef hrtc;

/* RTC init function */
void MX_RTC_Init(void)
{
  RTC_TimeTypeDef sTime = {0};
  RTC_DateTypeDef sDate = {0};

  /** Initialize RTC Only 
  */
  hrtc.Instance = RTC;
  hrtc.Init.HourFormat = RTC_HOURFORMAT_24;
  hrtc.Init.AsynchPrediv = 127;
  hrtc.Init.SynchPrediv = 255;
  hrtc.Init.OutPut = RTC_OUTPUT_DISABLE;
  hrtc.Init.OutPutRemap = RTC_OUTPUT_REMAP_NONE;
  hrtc.Init.OutPutPolarity = RTC_OUTPUT_POLARITY_HIGH;
  hrtc.Init.OutPutType = RTC_OUTPUT_TYPE_OPENDRAIN;
  if (HAL_RTC_Init(&hrtc) != HAL_OK)
  {
    Error_Handler();
  }

  /** Initialize RTC and set the Time and Date 
  */
  sTime.Hours = 0x0;
  sTime.Minutes = 0x0;
  sTime.Seconds = 0x0;
  sTime.DayLightSaving = RTC_DAYLIGHTSAVING_NONE;
  sTime.StoreOperation = RTC_STOREOPERATION_RESET;
  if (HAL_RTC_SetTime(&hrtc, &sTime, RTC_FORMAT_BCD) != HAL_OK)
  {
    Error_Handler();
  }
  sDate.WeekDay = RTC_WEEKDAY_MONDAY;
  sDate.Month = RTC_MONTH_JANUARY;
  sDate.Date = 0x1;
  sDate.Year = 0x0;

  if (HAL_RTC_SetDate(&hrtc, &sDate, RTC_FORMAT_BCD) != HAL_OK)
  {
    Error_Handler();
  }
  /** Enable the WakeUp 
  */
  if (HAL_RTCEx_SetWakeUpTimer_IT(&hrtc, 1000, RTC_WAKEUPCLOCK_RTCCLK_DIV16) != HAL_OK)
  {
    Error_Handler();
  }

}

void HAL_RTC_MspInit(RTC_HandleTypeDef* rtcHandle)
{

  if(rtcHandle->Instance==RTC)
  {
    /* RTC clock enable */
    __HAL_RCC_RTC_ENABLE();

    /* RTC interrupt Init */
    HAL_NVIC_SetPriority(RTC_IRQn, 1, 0);
    HAL_NVIC_EnableIRQ(RTC_IRQn);
  }
}

void HAL_RTC_MspDeInit(RTC_HandleTypeDef* rtcHandle)
{

  if(rtcHandle->Instance==RTC)
  {
    /* Peripheral clock disable */
    __HAL_RCC_RTC_DISABLE();

    /* RTC interrupt Deinit */
    HAL_NVIC_DisableIRQ(RTC_IRQn);
  }
} 

/* USER CODE BEGIN 1 */

void Configure_RTC_Clock(void)
{
  RCC_OscInitTypeDef        RCC_OscInitStruct;
  RCC_PeriphCLKInitTypeDef  PeriphClkInitStruct;

#ifndef USE_STM32L0XX_NUCLEO
  __HAL_RCC_PWR_CLK_ENABLE();
#endif
  HAL_PWR_EnableBkUpAccess();

  RCC_OscInitStruct.OscillatorType =  RCC_OSCILLATORTYPE_LSI | RCC_OSCILLATORTYPE_LSE;
  RCC_OscInitStruct.PLL.PLLState = RCC_PLL_NONE;
  RCC_OscInitStruct.LSIState = RCC_LSI_ON;
  RCC_OscInitStruct.LSEState = RCC_LSE_OFF;
  HAL_RCC_OscConfig(&RCC_OscInitStruct);

  PeriphClkInitStruct.PeriphClockSelection = RCC_PERIPHCLK_RTC;
  PeriphClkInitStruct.RTCClockSelection = RCC_RTCCLKSOURCE_LSI;
  HAL_RCCEx_PeriphCLKConfig(&PeriphClkInitStruct);

  /* Enable RTC Clock */
  __HAL_RCC_RTC_ENABLE();

  HAL_NVIC_SetPriority(RTC_IRQn, 0x01, 0);
  HAL_NVIC_EnableIRQ(RTC_IRQn);
}

/*Set flags*/
void setRtcInUseFlag(uint8_t rtcInUse) {
	rtc_in_use = rtcInUse;
}

void setRtcIrqFlag(uint8_t rtcIrq) {
	rtc_irq = rtcIrq;
}

void setRtcInUseForCsFlag(uint8_t rtcInUseForCs) {
	rtc_in_use_for_cs = rtcInUseForCs;
}

void setNextRtcWakeUpFlag(uint32_t nextRtcWakeUp) {
	next_rtc_wakeup = nextRtcWakeUp;
}

void setRtcPrescFlag(uint16_t rtcPresc) {
	rtc_presc = rtcPresc;
}

/*Get flags*/ 
uint32_t getNextRtcWakeUpFlag(void) {
	return next_rtc_wakeup;
}

uint8_t getRtcInUseForCsFlag(void) {
	return rtc_in_use_for_cs;
}

uint8_t getRtcIrqFlag(void) {
	return rtc_irq;
}

uint8_t getRtcInUseFlag(void) {
	return rtc_in_use;
}

uint16_t getRtcPrescFlag(void) {
	return rtc_presc;
}

RTC_HandleTypeDef * getRtcHandler(void) {
	return &hrtc;
}

/* USER CODE END 1 */

/************************ (C) COPYRIGHT STMicroelectronics *****END OF FILE****/
