hendrickbg/covid19_mon_track/Firmware_Project/Vaccine_Tracker_BLE/Drivers/Peripherals_Drivers/Src/bluenrg_lp_hal_timebase_tim_template.c

/**
  ******************************************************************************
  * @file    bluenrg_lp_hal_timebase_tim_template.c 
  * @author  RF Application Team
  * @brief   HAL time base based on the hardware TIM Template.
  *    
  *          This file overrides the native HAL time base functions (defined as weak)
  *          the TIM time base:
  *           + Intializes the TIM peripheral generate a Period elapsed Event each 1ms
  *           + HAL_IncTick is called inside HAL_TIM_PeriodElapsedCallback ie each 1ms
  * 
  ******************************************************************************
  * @attention
  *
  * <h2><center>&copy; Copyright (c) 2018 STMicroelectronics. 
  * All rights reserved.</center></h2>
  *
  * This software component is licensed by ST under BSD 3-Clause license,
  * the "License"; You may not use this file except in compliance with the 
  * License. You may obtain a copy of the License at:
  *                        opensource.org/licenses/BSD-3-Clause
  *
  ******************************************************************************
  */

/* Includes ------------------------------------------------------------------*/
#include "bluenrg_lp_hal.h"
#include "bluenrg_lp_hal_tim.h"
/** @addtogroup BLUENRG_LP_HAL_Driver
  * @{
  */

/** @addtogroup HAL_TimeBase_TIM
  * @{
  */ 

/* Private typedef -----------------------------------------------------------*/
/* Private define ------------------------------------------------------------*/
#define TIM1_CLK 64000000  /* TIM1 clock is an always 64 MHz */

/* Private macro -------------------------------------------------------------*/
/* Private variables ---------------------------------------------------------*/
extern TIM_HandleTypeDef TimHandle;
TIM_HandleTypeDef        TimHandle;
/* Private function prototypes -----------------------------------------------*/
void TIM1_IRQHandler(void);
/* Private functions ---------------------------------------------------------*/

/**
  * @brief  This function configures the TIM1 as a time base source. 
  *         The time source is configured to have 1ms time base with a dedicated 
  *         Tick interrupt priority. 
  * @note   This function is called  automatically at the beginning of program after
  *         reset by HAL_Init() or at any time when clock is configured, by HAL_RCC_ClockConfig(). 
  * @param  TickPriority: Tick interrupt priority.
  * @retval HAL status
  */
	
// HAL_StatusTypeDef HAL_InitTick (uint32_t TickPriority)
// {
//   //RCC_ClkInitTypeDef    clkconfig;
//   //uint32_t              uwTimclock, uwAPB1Prescaler;
//   uint32_t              uwPrescalerValue;
//   //uint32_t              pFLatency;
  
//     /*Configure the TIM1 IRQ priority */
//   HAL_NVIC_SetPriority(TIM1_IRQn, TickPriority);
  
//   /* Enable the TIM1 global Interrupt */
//   HAL_NVIC_EnableIRQ(TIM1_IRQn);
  
//   /* Enable TIM1 clock */
//   __HAL_RCC_TIM1_CLK_ENABLE();

//   /* Compute the prescaler value to have TIM1 counter clock equal to 1MHz */
//   uwPrescalerValue = (uint32_t) ((TIM1_CLK / 1000000U) - 1U);
  
//   /* Initialize TIM1 */
//   TimHandle.Instance = TIM1;
  
//   /* Initialize TIMx peripheral as follow:
//   + Period = [(TIM1CLK/1000) - 1]. to have a (1/1000) s time base.
//   + Prescaler = (uwTimclock/1000000 - 1) to have a 1MHz counter clock.
//   + ClockDivision = 0
//   + Counter direction = Up
//   */
//   TimHandle.Init.Period = (1000000U / 1000U) - 1U;
//   TimHandle.Init.Prescaler = uwPrescalerValue;
//   TimHandle.Init.ClockDivision = 0U;
//   TimHandle.Init.CounterMode = TIM_COUNTERMODE_UP;
//   if(HAL_TIM_Base_Init(&TimHandle) == HAL_OK)
//   {
//     /* Start the TIM time Base generation in interrupt mode */
//     return HAL_TIM_Base_Start_IT(&TimHandle);
//   }
  
//   /* Return function status */
//   return HAL_ERROR;
// }

/**
  * @brief  Period elapsed callback in non blocking mode
  * @note   This function is called  when TIM1 interrupt took place, inside
  * HAL_TIM_IRQHandler(). It makes a direct call to HAL_IncTick() to increment
  * a global variable "uwTick" used as application time base.
  * @param  htim : TIM handle
  * @retval None
  */
void HAL_TIM_PeriodElapsedCallback(TIM_HandleTypeDef *htim)
{
  HAL_IncTick();
}

/**
  * @brief  This function handles TIM interrupt request.
  * @retval None
  */
/*void TIM1_IRQHandler(void)
{
  HAL_TIM_IRQHandler(&TimHandle);
}*/

/**
  * @}
  */ 

/**
  * @}
  */ 

/************************ (C) COPYRIGHT STMicroelectronics *****END OF FILE****/
