hendrickbg/covid19_mon_track/Firmware_Project/Vaccine_Tracker_BLE/Drivers/Peripherals_Drivers/Src/bluenrg_lp_ll_utils.c

/**
  ******************************************************************************
  * @file    bluenrg_lp_ll_utils.c
  * @author  RF Application Team
  * @brief   UTILS LL module driver.
  ******************************************************************************
  * @attention
  *
  * <h2><center>&copy; Copyright (c) 2018 STMicroelectronics. 
  * All rights reserved.</center></h2>
  *
  * This software component is licensed by ST under BSD 3-Clause license,
  * the "License"; You may not use this file except in compliance with the 
  * License. You may obtain a copy of the License at:
  *                        opensource.org/licenses/BSD-3-Clause
  *
  ******************************************************************************
  */
/* Includes ------------------------------------------------------------------*/
#include "bluenrg_lp_ll_utils.h"
#include "bluenrg_lp_ll_rcc.h"
#include "bluenrg_lp_ll_system.h"
#include "bluenrg_lp_ll_pwr.h"
#ifdef  USE_FULL_ASSERT
#include "bluenrg_lp_assert.h"
#else
#define assert_param(expr) ((void)0U)
#endif

/** @addtogroup BLUENRG_LP_LL_Driver
  * @{
  */

/** @addtogroup UTILS_LL
  * @{
  */

/* Private types -------------------------------------------------------------*/
/* Private variables ---------------------------------------------------------*/
/* Private constants ---------------------------------------------------------*/
/** @addtogroup UTILS_LL_Private_Constants
  * @{
  */

/**
  * @}
  */

/* Private macros ------------------------------------------------------------*/
/* Private function prototypes -----------------------------------------------*/
/* Exported functions --------------------------------------------------------*/
/** @addtogroup UTILS_LL_Exported_Functions
  * @{
  */

/** @addtogroup UTILS_LL_EF_DELAY
  * @{
  */

/**
  * @brief  This function configures the Cortex-M SysTick source to have 1ms time base.
  * @note   When a RTOS is used, it is recommended to avoid changing the Systick
  *         configuration by calling this function, for a delay use rather osDelay RTOS service.
  * @param  HCLKFrequency HCLK frequency in Hz
  * @note   HCLK frequency can be calculated thanks to RCC helper macro or function @ref LL_RCC_GetSystemClocksFreq (HCLK2_Frequency field)
  * @retval None
  */
void LL_Init1msTick(uint32_t HCLKFrequency)
{
  /* Use frequency provided in argument */
  LL_InitTick(HCLKFrequency, 1000);
}


/**
  * @brief  This function provides accurate delay (in milliseconds) based
  *         on SysTick counter flag
  * @note   When a RTOS is used, it is recommended to avoid using blocking delay
  *         and use rather osDelay service.
  * @note   To respect 1ms timebase, user should call @ref LL_Init1msTick function which
  *         will configure Systick to 1ms
  * @param  Delay specifies the delay time length, in milliseconds.
  * @retval None
  */
void LL_mDelay(uint32_t Delay)
{
  uint32_t mDelay = Delay;
  __IO uint32_t  tmp = SysTick->CTRL;  /* Clear the COUNTFLAG first */
  /* Add this code to indicate that local variable is not used */
  ((void)tmp);

  /* Add a period to guaranty minimum wait */
  if (mDelay < LL_MAX_DELAY)
  {
     mDelay++;
  }

  while (mDelay != 0U)
  {
    if ((SysTick->CTRL & SysTick_CTRL_COUNTFLAG_Msk) != 0U)
    {
      mDelay--;
    }
  }
}

/**
  * @}
  */

/**
  * @brief  This function sets directly SystemCoreClock CMSIS variable.
  * @note   Variable can be calculated also through function.
  * @param  HCLKFrequency HCLK frequency in Hz (can be calculated thanks to RCC helper macro or function @ref LL_RCC_GetSystemClocksFreq )
  * @retval None
  */
void LL_SetSystemCoreClock(uint32_t HCLKFrequency)
{
  /* HCLK clock frequency */
  SystemCoreClock = HCLKFrequency;
}
/**
  * @}
  */


/**
  * @}
  */



/**
  * @}
  */


/************************ (C) COPYRIGHT STMicroelectronics *****END OF FILE****/
